hcodu/Barracks-LED-Sign/3D MODELS/inserts/C insert.stl

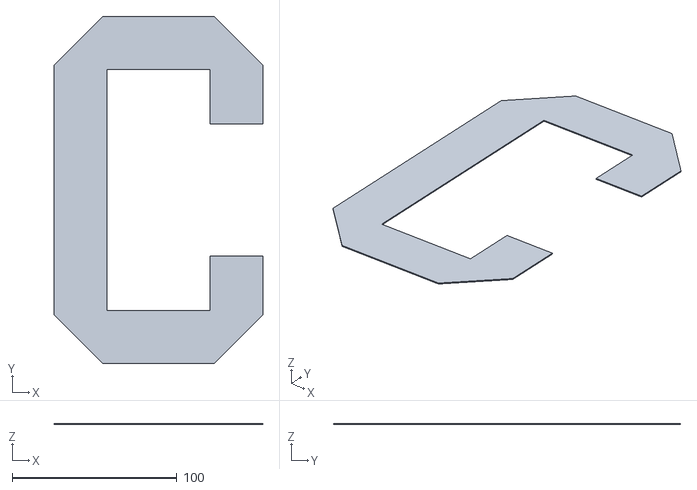
[picture p17: CAD file, 2026-07-22]
3D MODELS/inserts/C insert.stl
126.6 x 210.5 x 0.6
