hcodu/Barracks-LED-Sign/3D MODELS/stands/B stand.stl

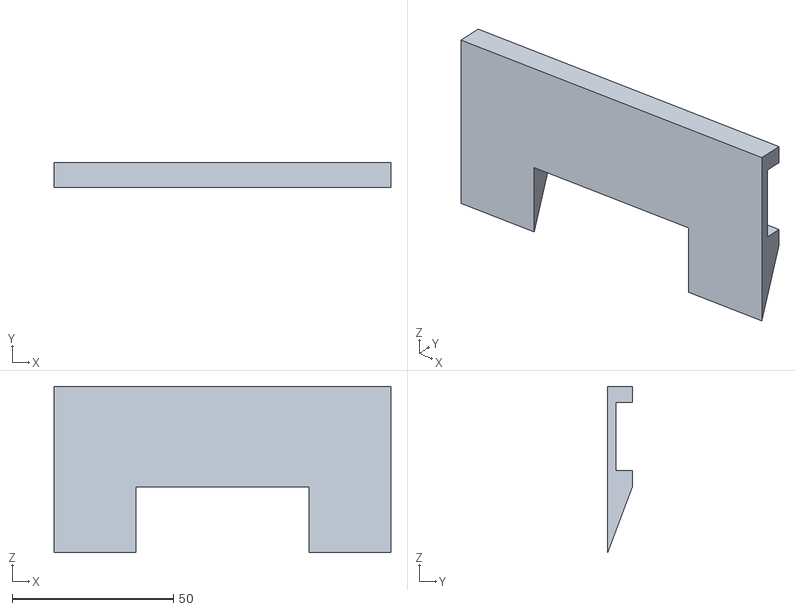
[picture p18: CAD file, 2026-07-22]
3D MODELS/stands/B stand.stl
104.4 x 7.62 x 51.6
