hcodu/Barracks-LED-Sign/3D MODELS/v2 stands/RR Stand.stl

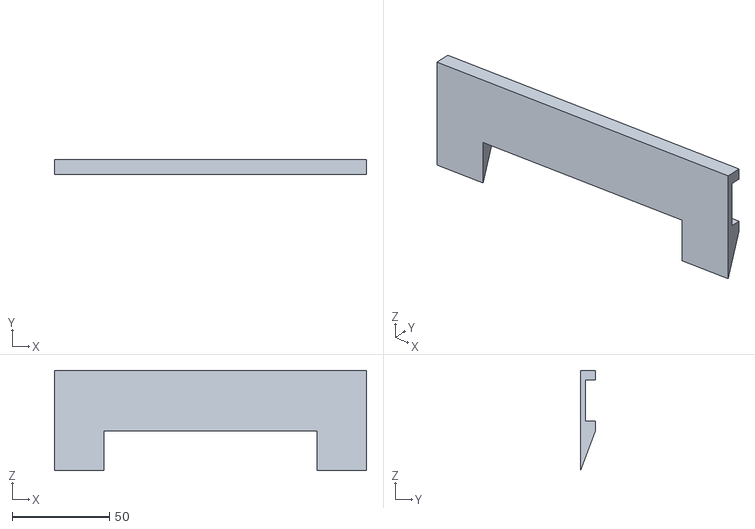
[picture p19: CAD file, 2026-07-22]
3D MODELS/v2 stands/RR Stand.stl
160.4 x 7.62 x 51.6
