hcodu/Barracks-LED-Sign/3D MODELS/backings/K back 1.stl

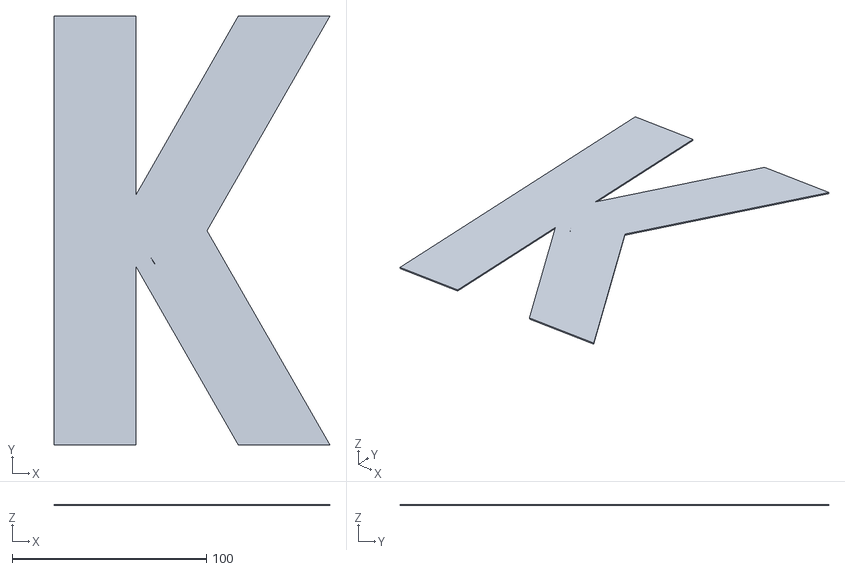
[picture p20: CAD file, 2026-07-22]
3D MODELS/backings/K back 1.stl
141.9 x 220.6 x 0.762
