hcodu/Barracks-LED-Sign/3D MODELS/inserts/R insert v2.stl

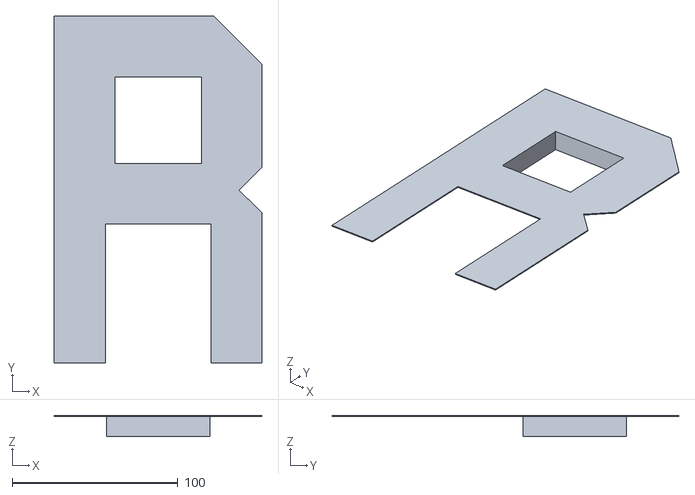
[picture p21: CAD file, 2026-07-22]
3D MODELS/inserts/R insert v2.stl
125.5 x 209.4 x 12.7
