hcodu/Barracks-LED-Sign/3D MODELS/backings/A back 1.stl

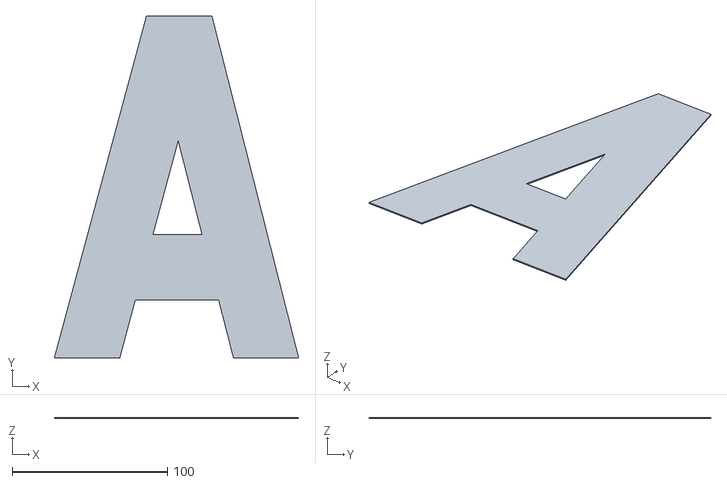
[picture p22: CAD file, 2026-07-22]
3D MODELS/backings/A back 1.stl
157.7 x 220.6 x 0.762
