hcodu/Barracks-LED-Sign/3D MODELS/inserts/R insert 2.stl

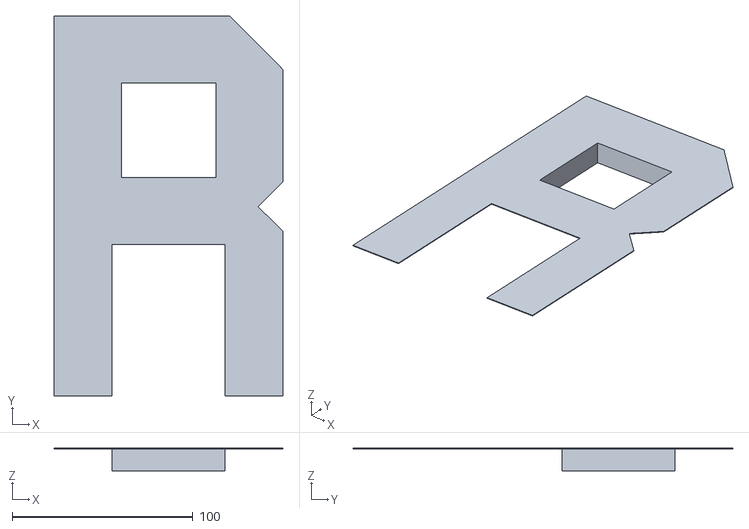
[picture p24: CAD file, 2026-07-22]
3D MODELS/inserts/R insert 2.stl
126.6 x 210.5 x 12.7
