hcodu/Barracks-LED-Sign/3D MODELS/stands/C stand.stl

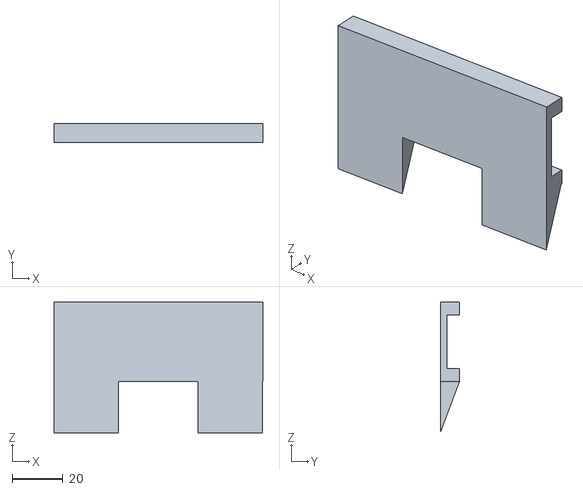
[picture p25: CAD file, 2026-07-22]
3D MODELS/stands/C stand.stl
82.6 x 7.62 x 51.6
