hcodu/Barracks-LED-Sign/3D MODELS/backings/B back.stl

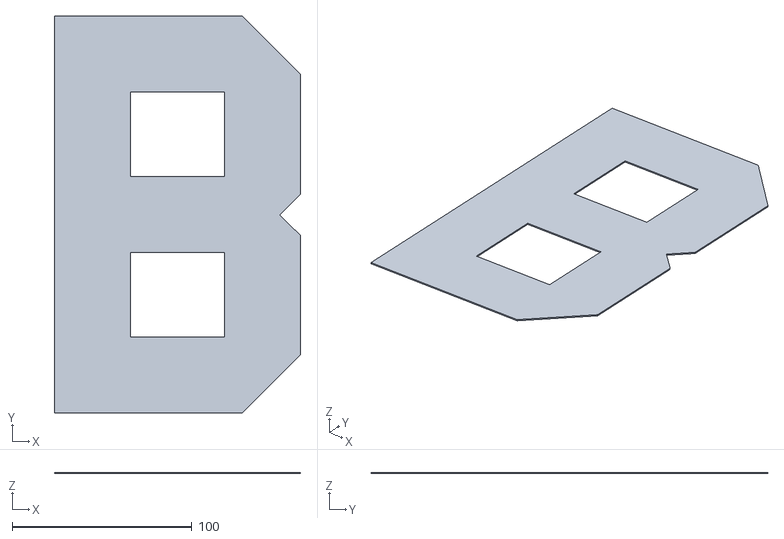
[picture p26: CAD file, 2026-07-22]
3D MODELS/backings/B back.stl
136.7 x 220.6 x 0.762
