hcodu/Barracks-LED-Sign/3D MODELS/frames/S frame.stl

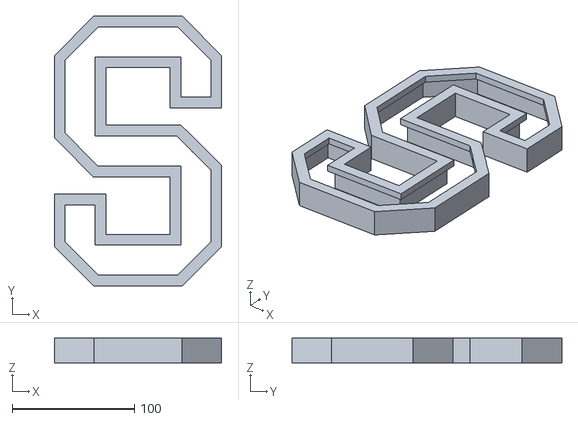
[picture p27: CAD file, 2026-07-22]
3D MODELS/frames/S frame.stl
136.7 x 220.6 x 20.3
