hcodu/Barracks-LED-Sign/3D MODELS/inserts/A insert v2.stl

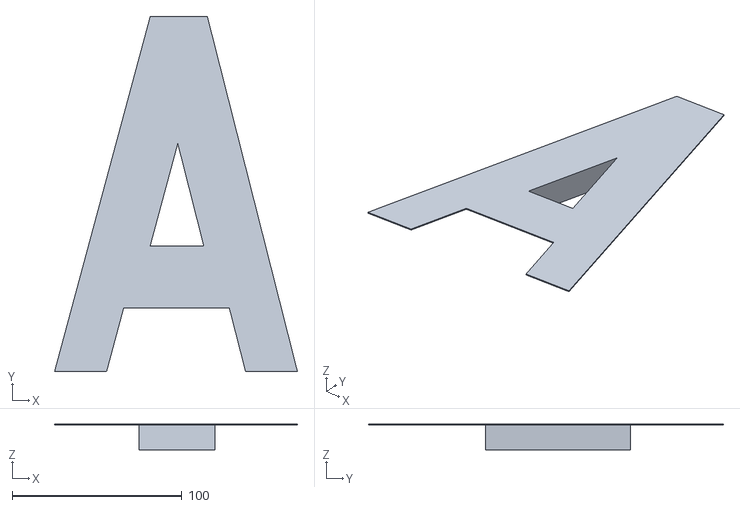
[picture p28: CAD file, 2026-07-22]
3D MODELS/inserts/A insert v2.stl
143.2 x 209.4 x 15.2
