hcodu/Barracks-LED-Sign/3D MODELS/v2 stands/BA_Stand.stl

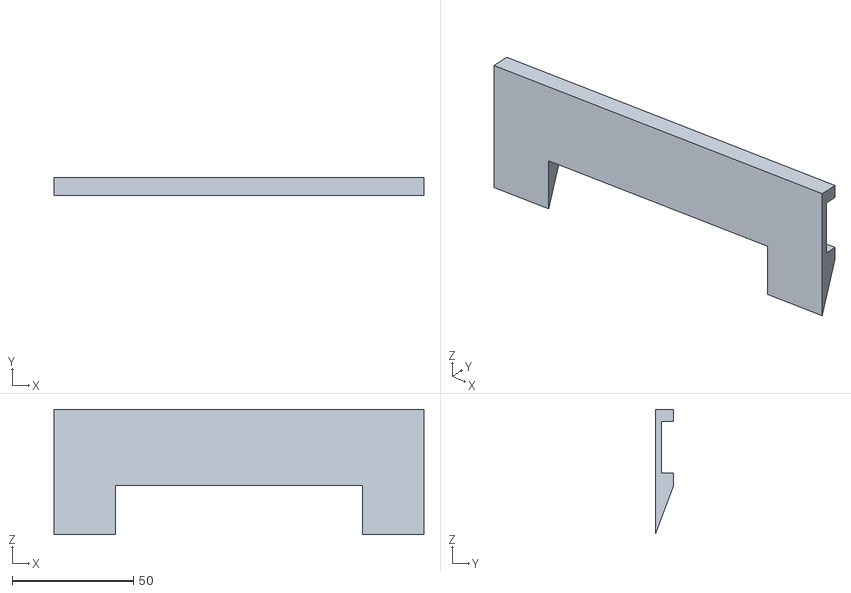
[picture p29: CAD file, 2026-07-22]
3D MODELS/v2 stands/BA_Stand.stl
152.4 x 7.62 x 51.6
