hcodu/Barracks-LED-Sign/3D MODELS/frames/C frame.stl

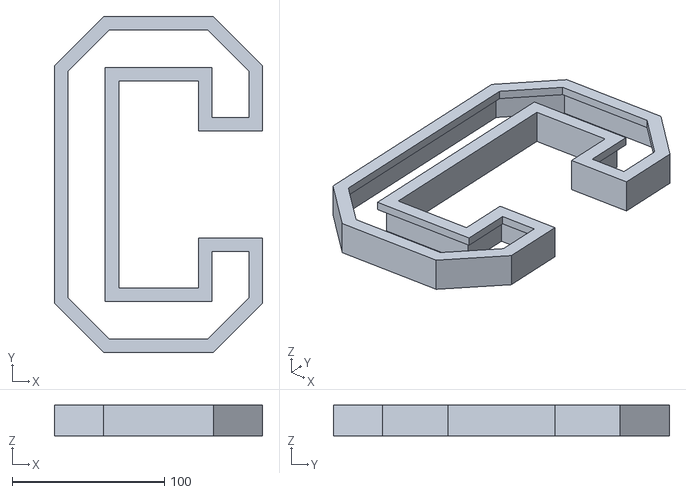
[picture p30: CAD file, 2026-07-22]
3D MODELS/frames/C frame.stl
136.7 x 220.6 x 20.3
