hcodu/Barracks-LED-Sign/3D MODELS/inserts/C insert v2.stl

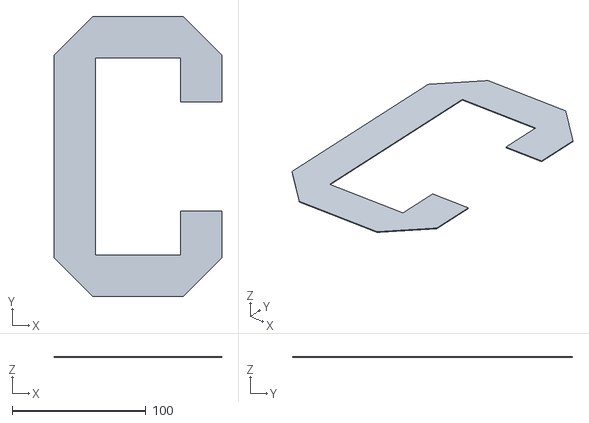
[picture p31: CAD file, 2026-07-22]
3D MODELS/inserts/C insert v2.stl
125.5 x 209.4 x 0.6
