hcodu/Barracks-LED-Sign/3D MODELS/v2 stands/AC Stand.stl

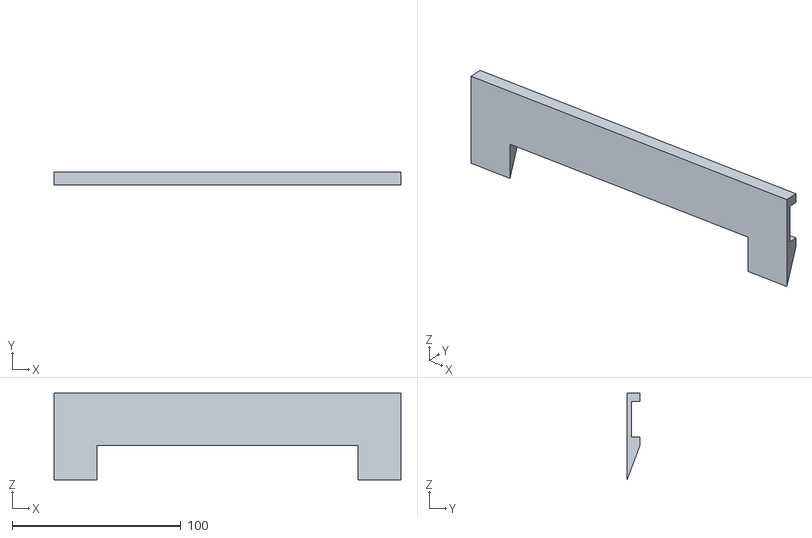
[picture p32: CAD file, 2026-07-22]
3D MODELS/v2 stands/AC Stand.stl
205.8 x 7.62 x 51.6
