hcodu/Barracks-LED-Sign/3D MODELS/inserts/S insert.stl

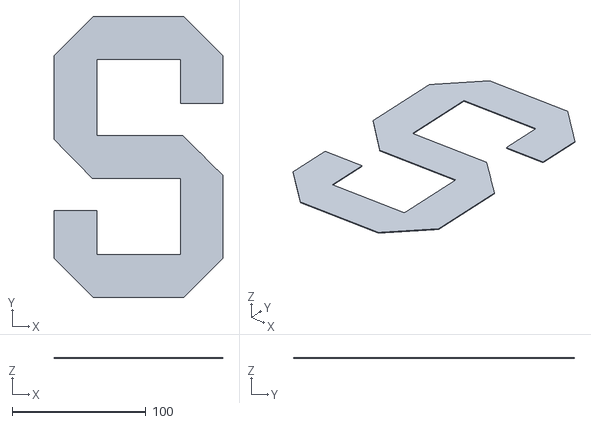
[picture p33: CAD file, 2026-07-22]
3D MODELS/inserts/S insert.stl
126.6 x 210.5 x 0.6
