hcodu/Barracks-LED-Sign/3D MODELS/inserts/K insert v2.stl

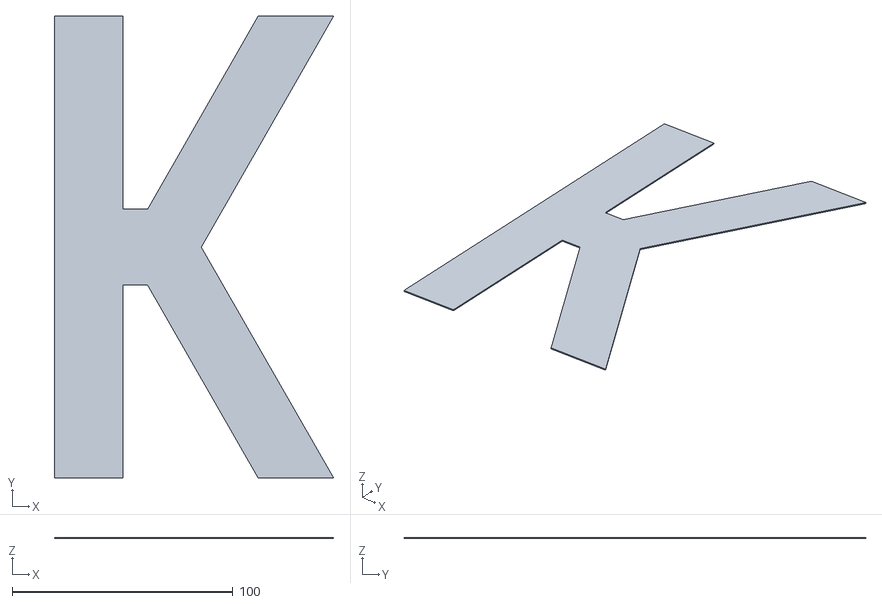
[picture p34: CAD file, 2026-07-22]
3D MODELS/inserts/K insert v2.stl
126.7 x 209.4 x 0.6
