hcodu/Barracks-LED-Sign/3D MODELS/inserts/K insert.stl

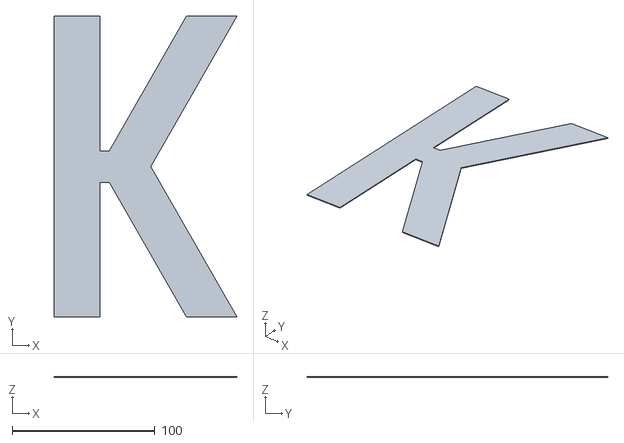
[picture p35: CAD file, 2026-07-22]
3D MODELS/inserts/K insert.stl
128.1 x 210.5 x 0.6
